iMike78/home-mini-DiP-v1/parts/MAX98357AETE_T.step

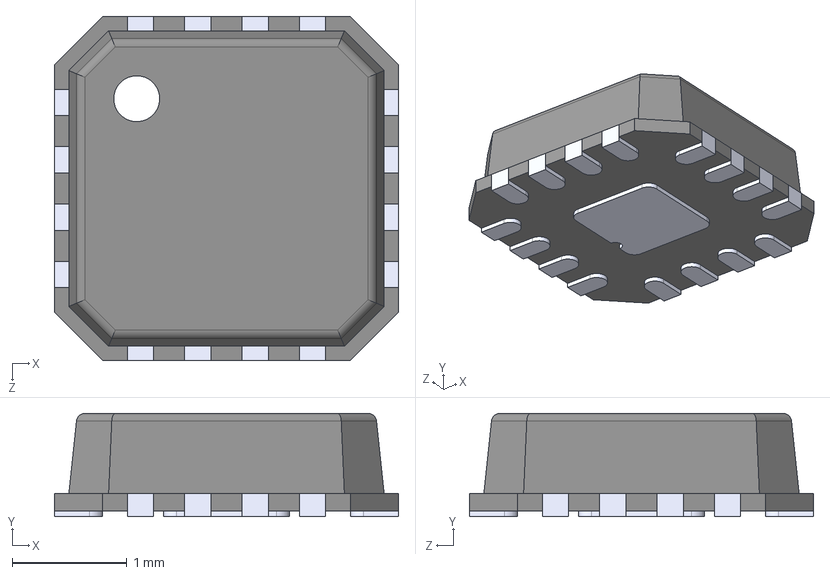
[picture p20: CAD file, 2025-12-22]
parts/MAX98357AETE_T.step
3.00 x 0.9 x 3.00 mm
