iMike78/home-mini-DiP-v1/parts/1775443-2.stp

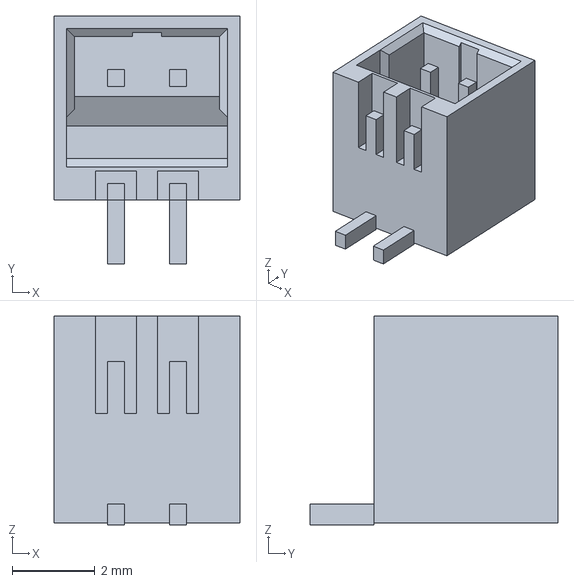
[picture p21: CAD file, 2025-12-22]
parts/1775443-2.stp
4.50 x 6.00 x 5.05 mm
