iMike78/home-mini-DiP-v1/audio.kicad_sch

## KiCad design audio.kicad_sch (2026-02-12)

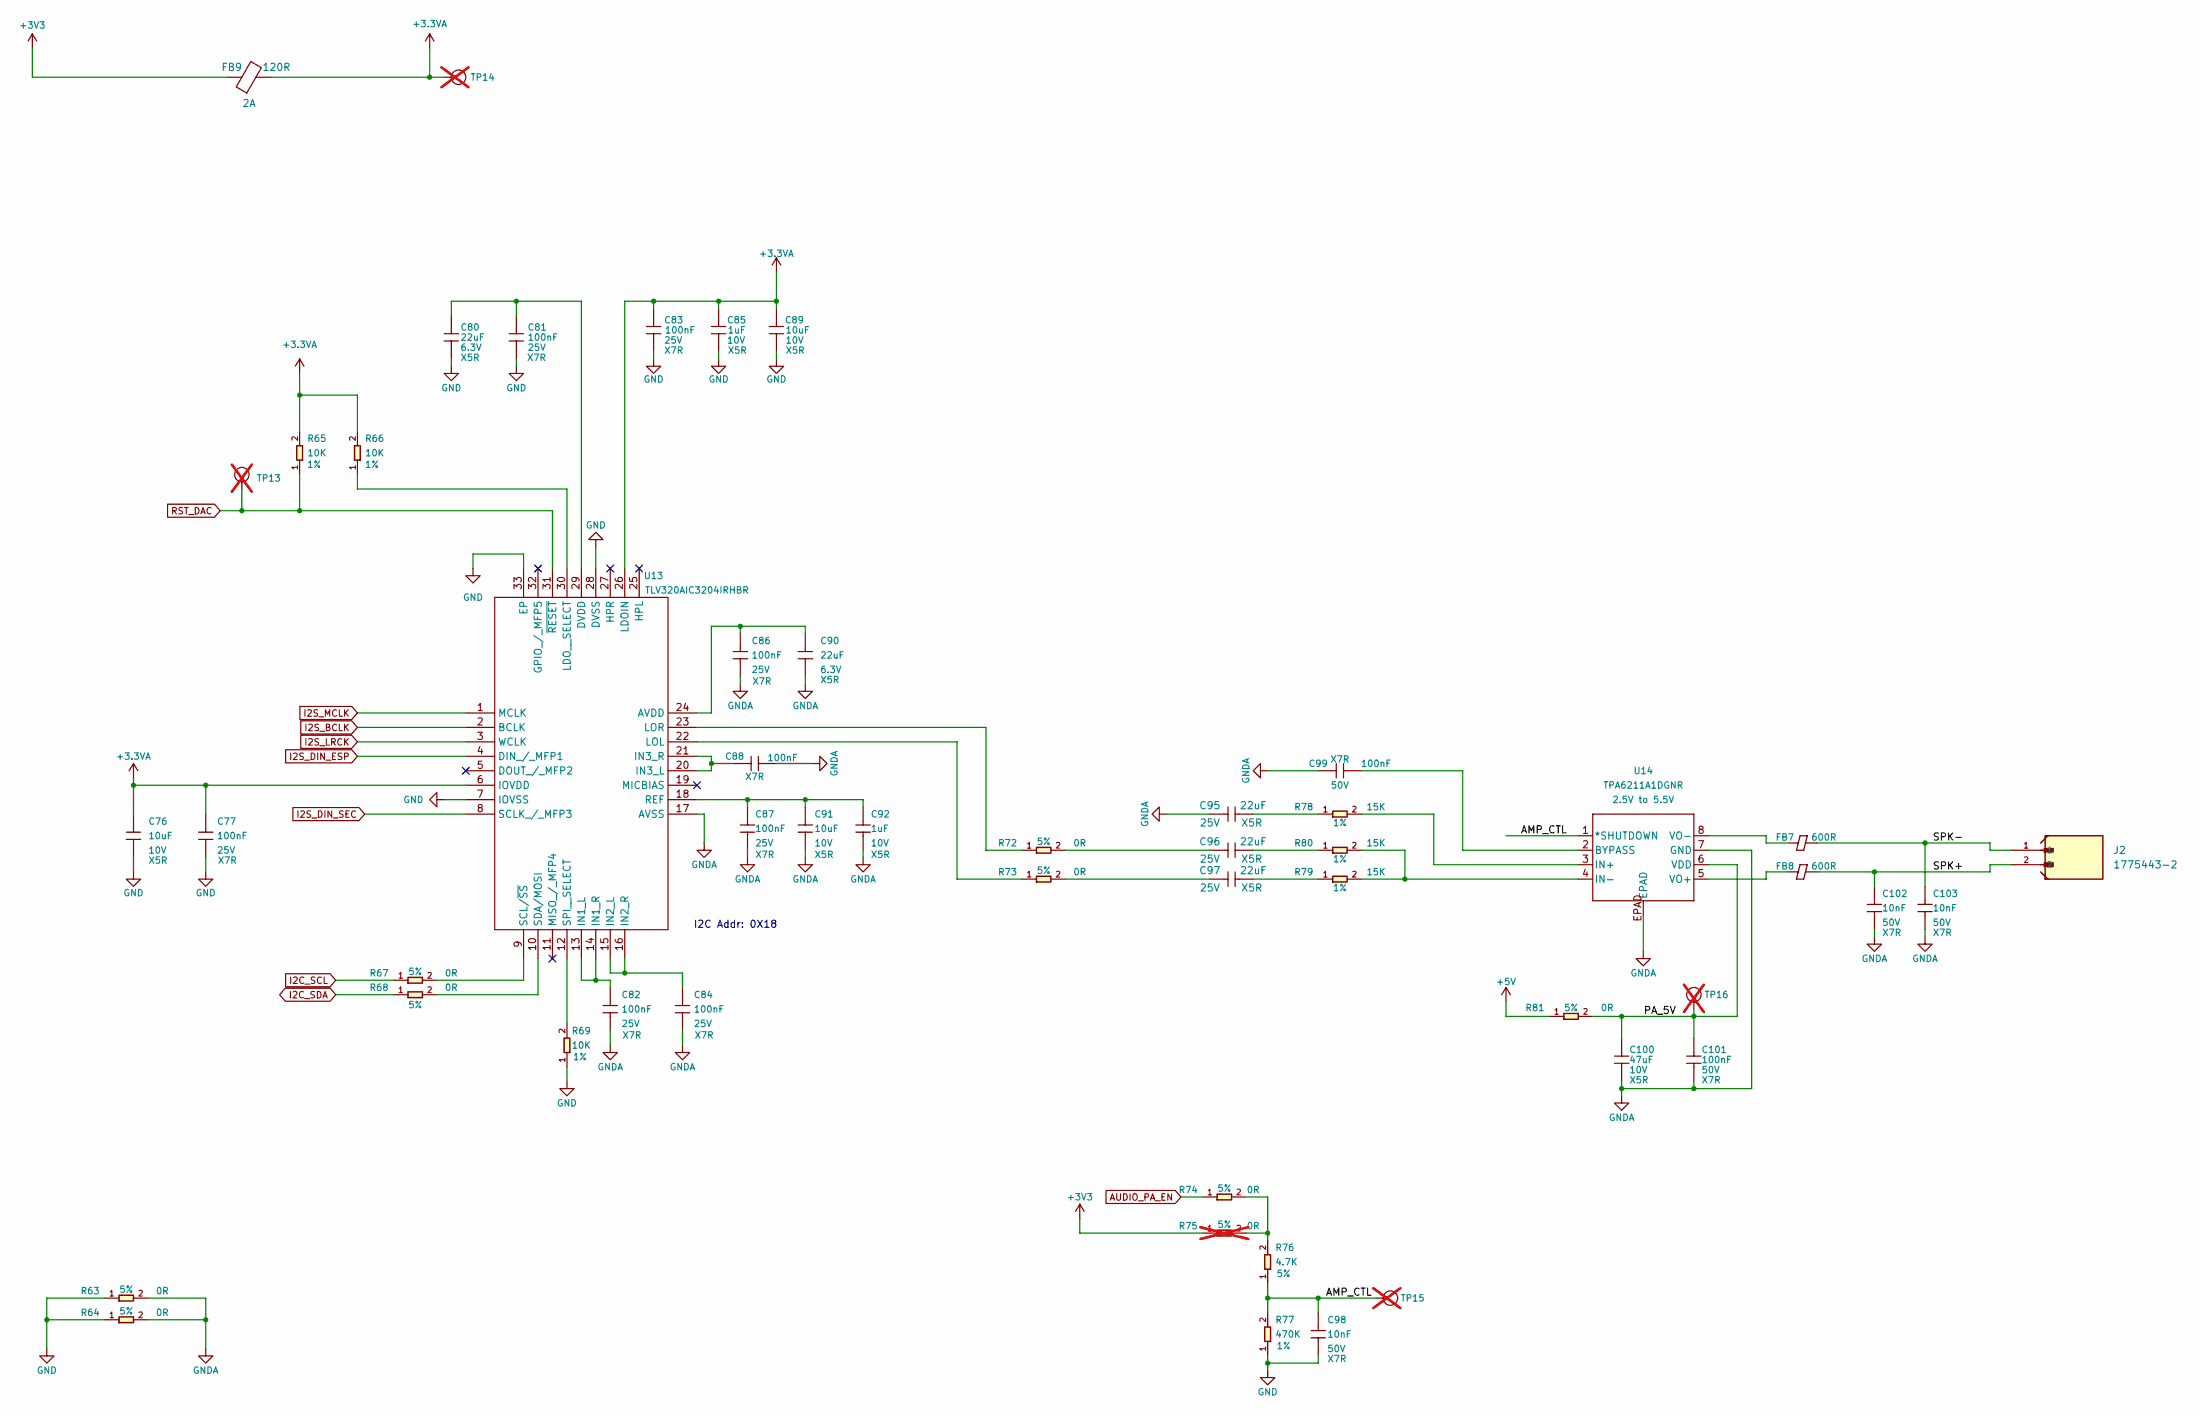
[picture p22: schematic audio.kicad_sch]

Parts:
C76, C89, C91: 10uF; C_0603_1608Metric; Voltage Rating 10V; Voltage 10V; MPN CL10A106KP8NNNC; LCSC Part # C19702
C77, C81, C82, C83, C84, C86, C87, C88: 100nF; C_0402_1005Metric; Voltage Rating 25V; Voltage 16V; MPN CL05B104KO5NNNC; LCSC Part # C1525
C80, C90: 22uF; C_0603_1608Metric; Voltage Rating 6.3V; Voltage 6.3V; MPN CL10A226MQ8NRNC; LCSC Part # C59461
C85, C92: 1uF; C_0402_1005Metric; Voltage Rating 10V; MPN CL05A105KA5NQNC; LCSC Part # C52923
C95, C96, C97: 22uF; C_0805_2012Metric; Voltage Rating 25V; Voltage 25V; MPN CL21A226MAQNNNE; LCSC Part # C45783
C98, C102, C103: 10nF; C_0402_1005Metric; Voltage Rating 50V; Voltage 50V; MPN CL05B103KB5NNNC; LCSC Part # C15195
C99, C101: 100nF; C_0603_1608Metric; Voltage Rating 50V; Voltage 50V; MPN CC0603KRX7R9BB104; LCSC Part # C14663
C100: 47uF; C_1206_3216Metric; Voltage Rating 10V; Voltage 10V; MPN CL31A476MPHNNNE; LCSC Part # C96123
FB7, FB8: 600R; BLM18PG121SN1D; Rating 500mA; MPN BLM18KG601SN1D; LCSC Part # C85833
FB9: 120R; BLM18PG121SN1D; Part number BLM18PG121SN1D; LCSC Part # C14709
J2: 1775443-2; PARTREV B5; LCSC Part # C5162845
R63, R64, R67, R68, R72, R73, R74: 0R; R_0402_1005Metric; Tolerance 5%; MPN 0402WGF0000TCE; LCSC Part # C17168
R65, R66, R69: 10K; R_0402_1005Metric; Tolerance 1%; MPN 0402WGF1002TCE; LCSC Part # C25744
R75: 0R; R_0402_1005Metric; Tolerance 5%; MPN RC0402JR-070RL; not fitted
R76: 4.7K; R_0402_1005Metric; Tolerance 5%; MPN 0402WGF4701TCE; LCSC Part # C25900
R77: 470K; R_0402_1005Metric; Tolerance 1%; Manufacturer Part 0402WGF4703TCE; LCSC Part # C25790
R78, R79, R80: 15K; R_0603_1608Metric; Tolerance 1%; Manufacturer Part 0603WAF1502T5E; LCSC Part # C22809
R81: 0R; R_0603_1608Metric; Tolerance 5%; Manufacturer Part 0603WAF0000T5E; LCSC Part # C21189
TP13, TP15: TEST-POINT; TestPoint_Pad_D1.0mm; not fitted
TP14, TP16: Test Point; TestPoint_Pad_D1.0mm; Part Type Test Point; not fitted
U13: TLV320AIC3204IRHBR; MPN TLV320AIC3204IRHBR; Mouser Part Number 595-V320AIC3204IRHBR
U14: TPA6211A1DGNR; Rating 2.5V to 5.5V; MPN TPA6211A1DGNR; LCSC Part # C7718

Connections:
+3.3VA: C76.1, C77.1, C83.1, C85.1, C89.1, FB9.2, R65.2, R66.2, TP14.1, U13.6 (IOVDD), U13.26 (LDOIN)
+3V3: FB9.1, R75.1
+5V: R81.1
AMP_CTL: C98.1, R76.1, R77.2, TP15.1, U14.1 (*SHUTDOWN)
AUDIO_PA_EN: R74.1
GND: C76.2, C77.2, C80.2, C81.2, C83.2, C85.2, C89.2, C98.2, R63.1, R64.1, R69.1, R77.1, U13.7 (IOVSS), U13.28 (DVSS), U13.33 (EP)
GNDA: C82.2, C84.2, C86.2, C87.2, C88.2, C90.2, C91.2, C92.2, C95.1, C99.1, C100.2, C101.2, C102.2, C103.2, R63.2, R64.2, U13.17 (AVSS), U14.7 (GND), U14.EPAD
I2C_SCL: R67.1
I2C_SDA: R68.1
I2S_BCLK: U13.2 (BCLK)
I2S_DIN_ESP: U13.4 (DIN_/_MFP1)
I2S_DIN_SEC: U13.8 (SCLK_/_MFP3)
I2S_LRCK: U13.3 (WCLK)
I2S_MCLK: U13.1 (MCLK)
unnamed: C80.1, C81.1, U13.29 (DVDD)
unnamed: C82.1, U13.13 (IN1_L), U13.14 (IN1_R)
unnamed: C84.1, U13.15 (IN2_L), U13.16 (IN2_R)
unnamed: C86.1, C90.1, U13.24 (AVDD)
unnamed: C87.1, C91.1, C92.1, U13.18 (REF)
unnamed: C88.1, U13.20 (IN3_L), U13.21 (IN3_R)
unnamed: C95.2, R78.1
unnamed: C96.1, R72.2
unnamed: C96.2, R80.1
unnamed: C97.1, R73.2
unnamed: C97.2, R79.1
unnamed: C99.2, U14.2 (BYPASS)
unnamed: FB7.1, U14.8 (VO-)
unnamed: FB8.1, U14.5 (VO+)
unnamed: R66.1, U13.30 (LDO__SELECT)
unnamed: R67.2, U13.9 (SCL/~SS)
unnamed: R68.2, U13.10 (SDA/MOSI)
unnamed: R69.2, U13.12 (SPI__SELECT)
unnamed: R72.1, U13.23 (LOR)
unnamed: R73.1, U13.22 (LOL)
unnamed: R74.2, R75.2, R76.2
unnamed: R78.2, U14.3 (IN+)
unnamed: R79.2, R80.2, U14.4 (IN-)
PA_5V: C100.1, C101.1, R81.2, TP16.1, U14.6 (VDD)
RST_DAC: R65.1, TP13.1, U13.31 (~RESET)
SPK+: C102.1, FB8.2, J2.2
SPK-: C103.1, FB7.2, J2.1

Notes on the sheet:
I2C Addr: 0X18
