iMike78/home-mini-DiP-v1/esp32.kicad_sch

## KiCad design esp32.kicad_sch (2026-02-12)

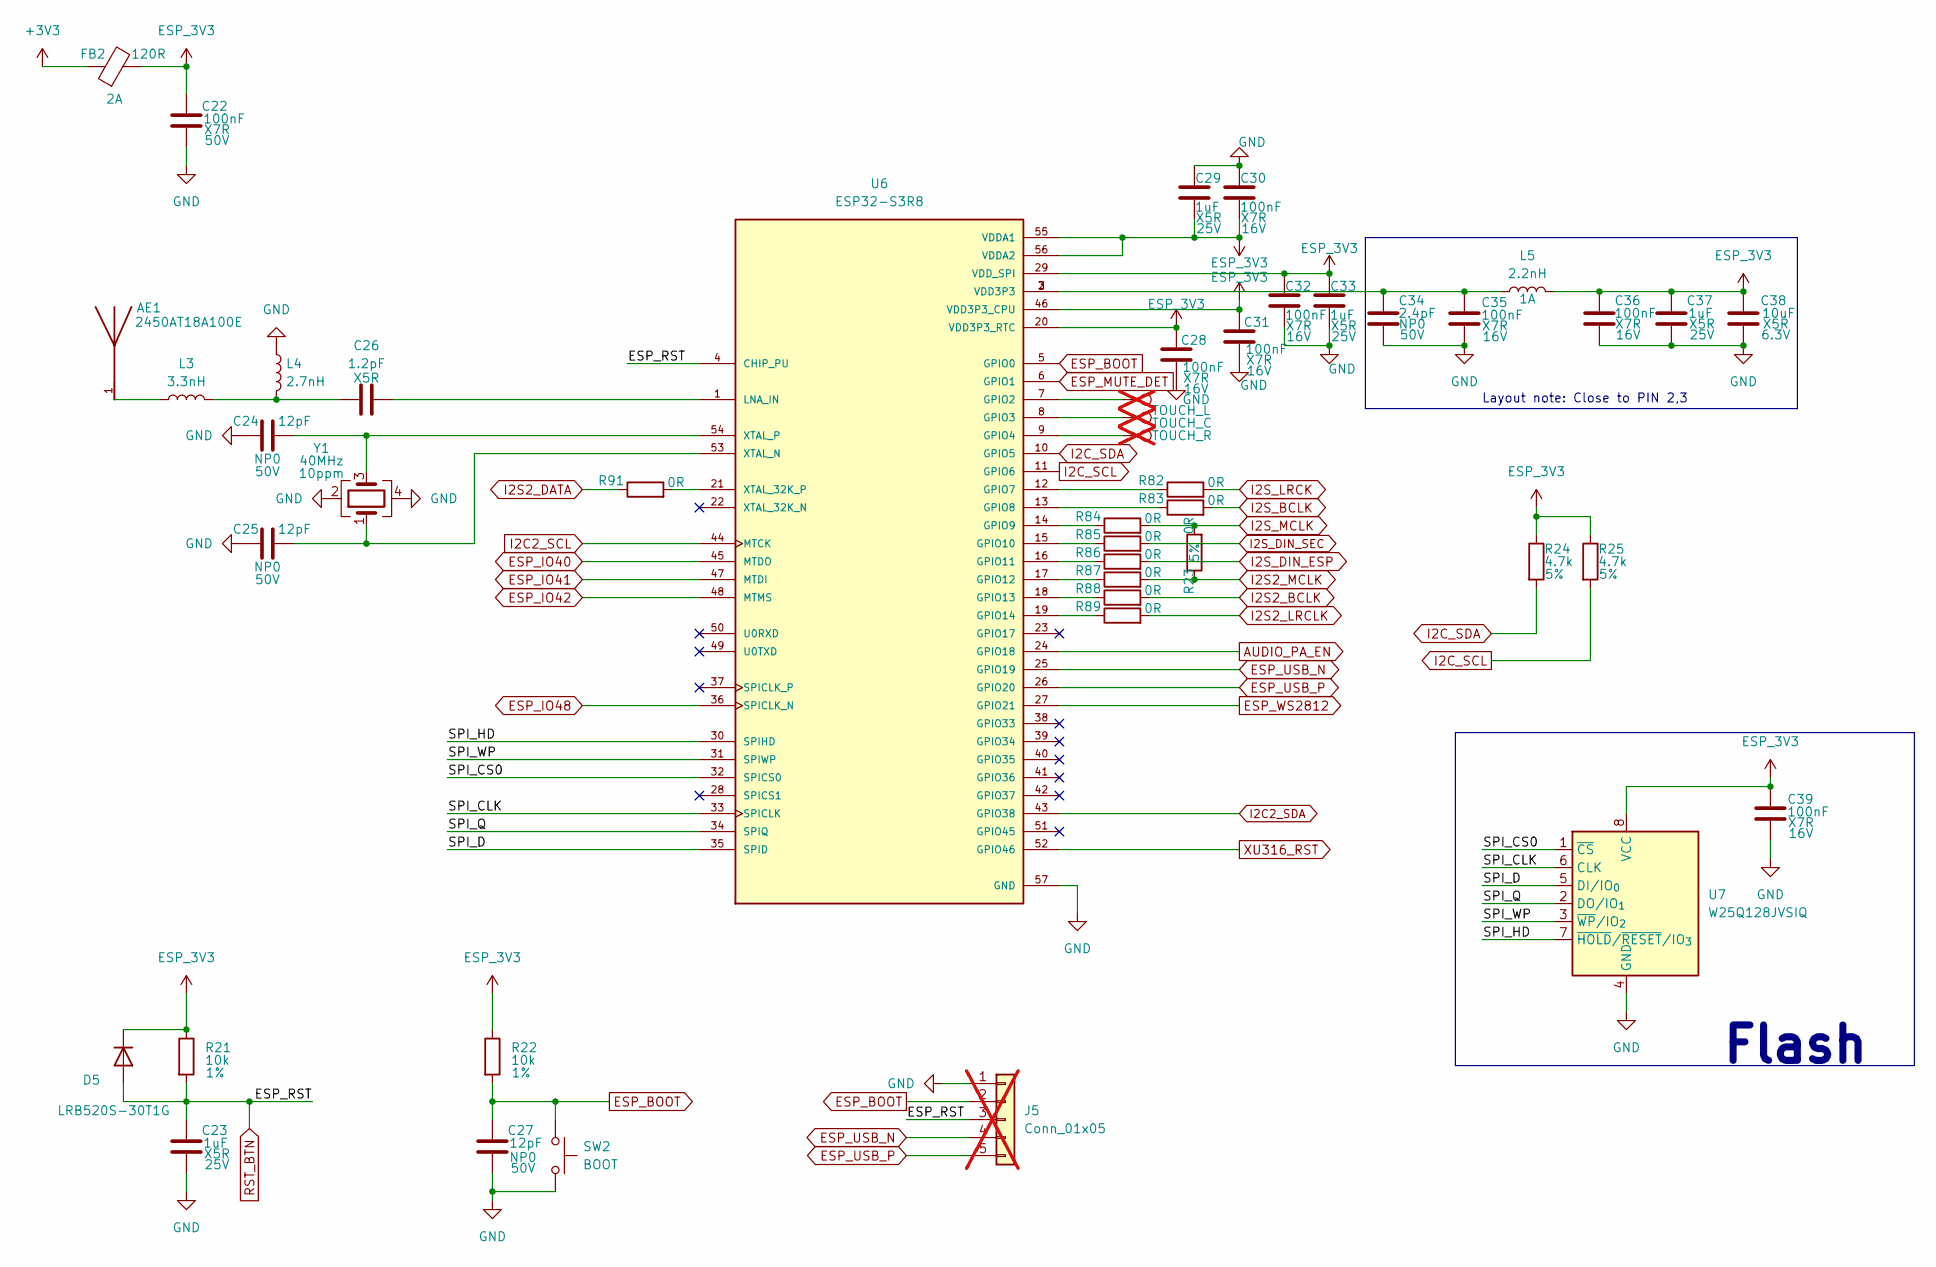
[picture p23: schematic esp32.kicad_sch]

Parts:
AE1: 2450AT18A100E; Johanson_2450AT18x100; PARTREV 1.3; LCSC Part # C89334
C22: 100nF; C_0603_1608Metric; Voltage 50V; Manufacturer Part CC0603KRX7R9BB104; LCSC Part # C14663
C23, C29, C33, C37: 1uF; C_0402_1005Metric; Voltage 25V; Manufacturer Part CL05A105KA5NQNC; LCSC Part # C52923
C24, C25, C27: 12pF; C_0402_1005Metric; Voltage 50V; Manufacturer Part 0402CG120J500NT; LCSC Part # C1547
C26: 1.2pF; C_0402_1005Metric; Voltage 10V; Manufacturer Part CC0402BRNPO9BN1R2; LCSC Part # C327292
C28, C30, C31, C32, C35, C36, C39: 100nF; C_0402_1005Metric; Voltage 16V; Manufacturer Part CL05B104KO5NNNC; LCSC Part # C1525
C34: 2.4pF; C_0402_1005Metric; Voltage 50V; Manufacturer Part 0402CG2R4C500NT; LCSC Part # C48346
C38: 10uF; C_0402_1005Metric; Voltage 6.3V; Manufacturer Part CL05A106MQ5NUNC; LCSC Part # C15525
D5: LRB520S-30T1G; D_SOD-523; Manufacturer Part LRB520S-30T1G; LCSC Part # C83680
FB2: 120R; BLM18PG121SN1D; Part number BLM18PG121SN1D; LCSC Part # C14709
J5: Conn_01x05; PinHeader_1x05_P2.54mm_Vertical; not fitted
L3: 3.3nH; L_0402_1005Metric; Manufacturer Part SDCL1005C3N3STDF; LCSC Part # C16526
L4: 2.7nH; L_0402_1005Metric; Manufacturer Part MHQ1005P2N7BT000; LCSC Part # C434826
L5: 2.2nH; L_0402_1005Metric; Manufacturer Part LQG15HS2N2B02D; LCSC Part # C162540
R21, R22: 10k; R_0402_1005Metric; Tolerance 1%; Manufacturer Part 0402WGF1002TCE; LCSC Part # C25744
R23, R82, R83, R84, R85, R86, R87, R88, R89, R91: 0R; R_0402_1005Metric; Tolerance 5%; Manufacturer Part 0402WGF0000TCE; LCSC Part # C17168
R24, R25: 4.7k; R_0402_1005Metric; Tolerance 5%; Manufacturer Part 0402WGF4701TCE; LCSC Part # C25900
SW2: BOOT; SW-SMD_4P-L4.2-W3.2-P2.15-LS4.5; Manufacturer Part PTS810SJS250SMTRLFS; LCSC Part # C221897
TP6: TOUCH_L; TestPoint_Pad_2.5x2.5mm; not fitted
TP7: TOUCH_C; TestPoint_Pad_2.5x2.5mm; not fitted
TP8: TOUCH_R; TestPoint_Pad_2.5x2.5mm; not fitted
U6: ESP32-S3R8; QFN40P700X700X90-57N; Manufacturer Part ESP32-S3R8; LCSC Part # C2913194
U7: W25Q128JVSIQ; SOIC-8_5.3x5.3mm_P1.27mm; Manufacturer Part W25Q128JVSIQ; LCSC Part # C97521
Y1: 40MHz; Crystal_SMD_2016-4Pin_2.0x1.6mm; Tolerance 10ppm; Manufacturer Part TAXM40M4ZCBCDT2T; LCSC Part # C424431

Connections:
+3V3: FB2.1
AUDIO_PA_EN: U6.24 (GPIO18)
ESP_3V3: C22.1, C28.1, C29.2, C30.2, C31.1, C32.1, C33.1, C36.1, C37.1, C38.1, C39.1, D5.1 (K), FB2.2, L5.2, R21.1, R22.1, R24.1, R25.1, U6.20 (VDD3P3_RTC), U6.29 (VDD_SPI), U6.46 (VDD3P3_CPU), U6.55 (VDDA1), U6.56 (VDDA2), U7.8 (VCC)
ESP_BOOT: C27.1, J5.2, R22.2, SW2.1, U6.5 (GPIO0)
ESP_IO40: U6.45 (MTDO)
ESP_IO41: U6.47 (MTDI)
ESP_IO42: U6.48 (MTMS)
ESP_IO48: U6.36 (SPICLK_N)
ESP_MUTE_DET: U6.6 (GPIO1)
ESP_USB_N: J5.4, U6.25 (GPIO19)
ESP_USB_P: J5.5, U6.26 (GPIO20)
ESP_WS2812: U6.27 (GPIO21)
GND: C22.2, C23.2, C24.1, C25.1, C27.2, C28.2, C29.1, C30.1, C31.2, C32.2, C33.2, C34.2, C35.2, C36.2, C37.2, C38.2, C39.2, J5.1, L4.1, SW2.2, U6.57 (GND), U7.4 (GND), Y1.2, Y1.4
I2C2_SCL: U6.44 (MTCK)
I2C2_SDA: U6.43 (GPIO38)
I2C_SCL: R25.2, U6.11 (GPIO6)
I2C_SDA: R24.2, U6.10 (GPIO5)
I2S2_BCLK: R88.2
I2S2_DATA: R91.1
I2S2_LRCLK: R89.2
I2S2_MCLK: R23.1, R87.2
I2S_BCLK: R83.2
I2S_DIN_ESP: R86.2
I2S_DIN_SEC: R85.2
I2S_LRCK: R82.2
I2S_MCLK: R23.2, R84.2
unnamed: AE1.1, L3.1
unnamed: C24.2, U6.54 (XTAL_P), Y1.3
unnamed: C25.2, U6.53 (XTAL_N), Y1.1
unnamed: C26.1, L3.2, L4.2
unnamed: C26.2, U6.1 (LNA_IN)
unnamed: C34.1, C35.1, L5.1, U6.2 (VDD3P3), U6.3 (VDD3P3)
unnamed: R82.1, U6.12 (GPIO7)
unnamed: R83.1, U6.13 (GPIO8)
unnamed: R84.1, U6.14 (GPIO9)
unnamed: R85.1, U6.15 (GPIO10)
unnamed: R86.1, U6.16 (GPIO11)
unnamed: R87.1, U6.17 (GPIO12)
unnamed: R88.1, U6.18 (GPIO13)
unnamed: R89.1, U6.19 (GPIO14)
unnamed: R91.2, U6.21 (XTAL_32K_P)
unnamed: TP6.1, U6.7 (GPIO2)
unnamed: TP7.1, U6.8 (GPIO3)
unnamed: TP8.1, U6.9 (GPIO4)
RST_BTN: C23.1, D5.2 (A), J5.3, R21.2, U6.4 (CHIP_PU)
SPI_CLK: U6.33 (SPICLK), U7.6 (CLK)
SPI_CS0: U6.32 (SPICS0), U7.1 (~CS)
SPI_D: U6.35 (SPID), U7.5 (DI/IO_{0})
SPI_HD: U6.30 (SPIHD), U7.7 (~HOLD/~RESET/IO_{3})
SPI_Q: U6.34 (SPIQ), U7.2 (DO/IO_{1})
SPI_WP: U6.31 (SPIWP), U7.3 (~WP/IO_{2})
XU316_RST: U6.52 (GPIO46)

Notes on the sheet:
Flash
Layout note: Close to PIN 2,3
