iMike78/home-mini-DiP-v1/leds.kicad_sch

## KiCad design leds.kicad_sch (2026-01-06)

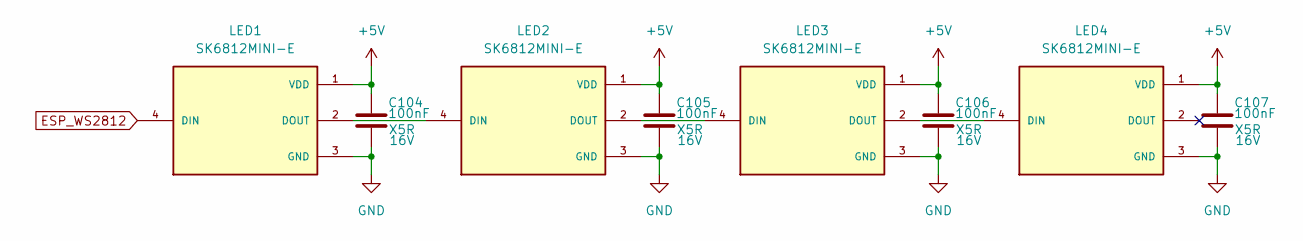
[picture p24: schematic leds.kicad_sch]

Parts:
C104, C105, C106, C107: 100nF; C_0402_1005Metric; Voltage 16V; Manufacturer Part CL05B104KO5NNNC; LCSC Part # C1525
LED1, LED2, LED3, LED4: SK6812MINI-E; PARTREV 2; LCSC Part # C5149201

Connections:
+5V: C104.1, C105.1, C106.1, C107.1, LED1.1 (VDD), LED2.1 (VDD), LED3.1 (VDD), LED4.1 (VDD)
ESP_WS2812: LED1.4 (DIN)
GND: C104.2, C105.2, C106.2, C107.2, LED1.3 (GND), LED2.3 (GND), LED3.3 (GND), LED4.3 (GND)
unnamed: LED1.2 (DOUT), LED2.4 (DIN)
unnamed: LED2.2 (DOUT), LED3.4 (DIN)
unnamed: LED3.2 (DOUT), LED4.4 (DIN)
