iMike78/home-mini-DiP-v1/power_handling.kicad_sch

## KiCad design power_handling.kicad_sch (2026-02-12)

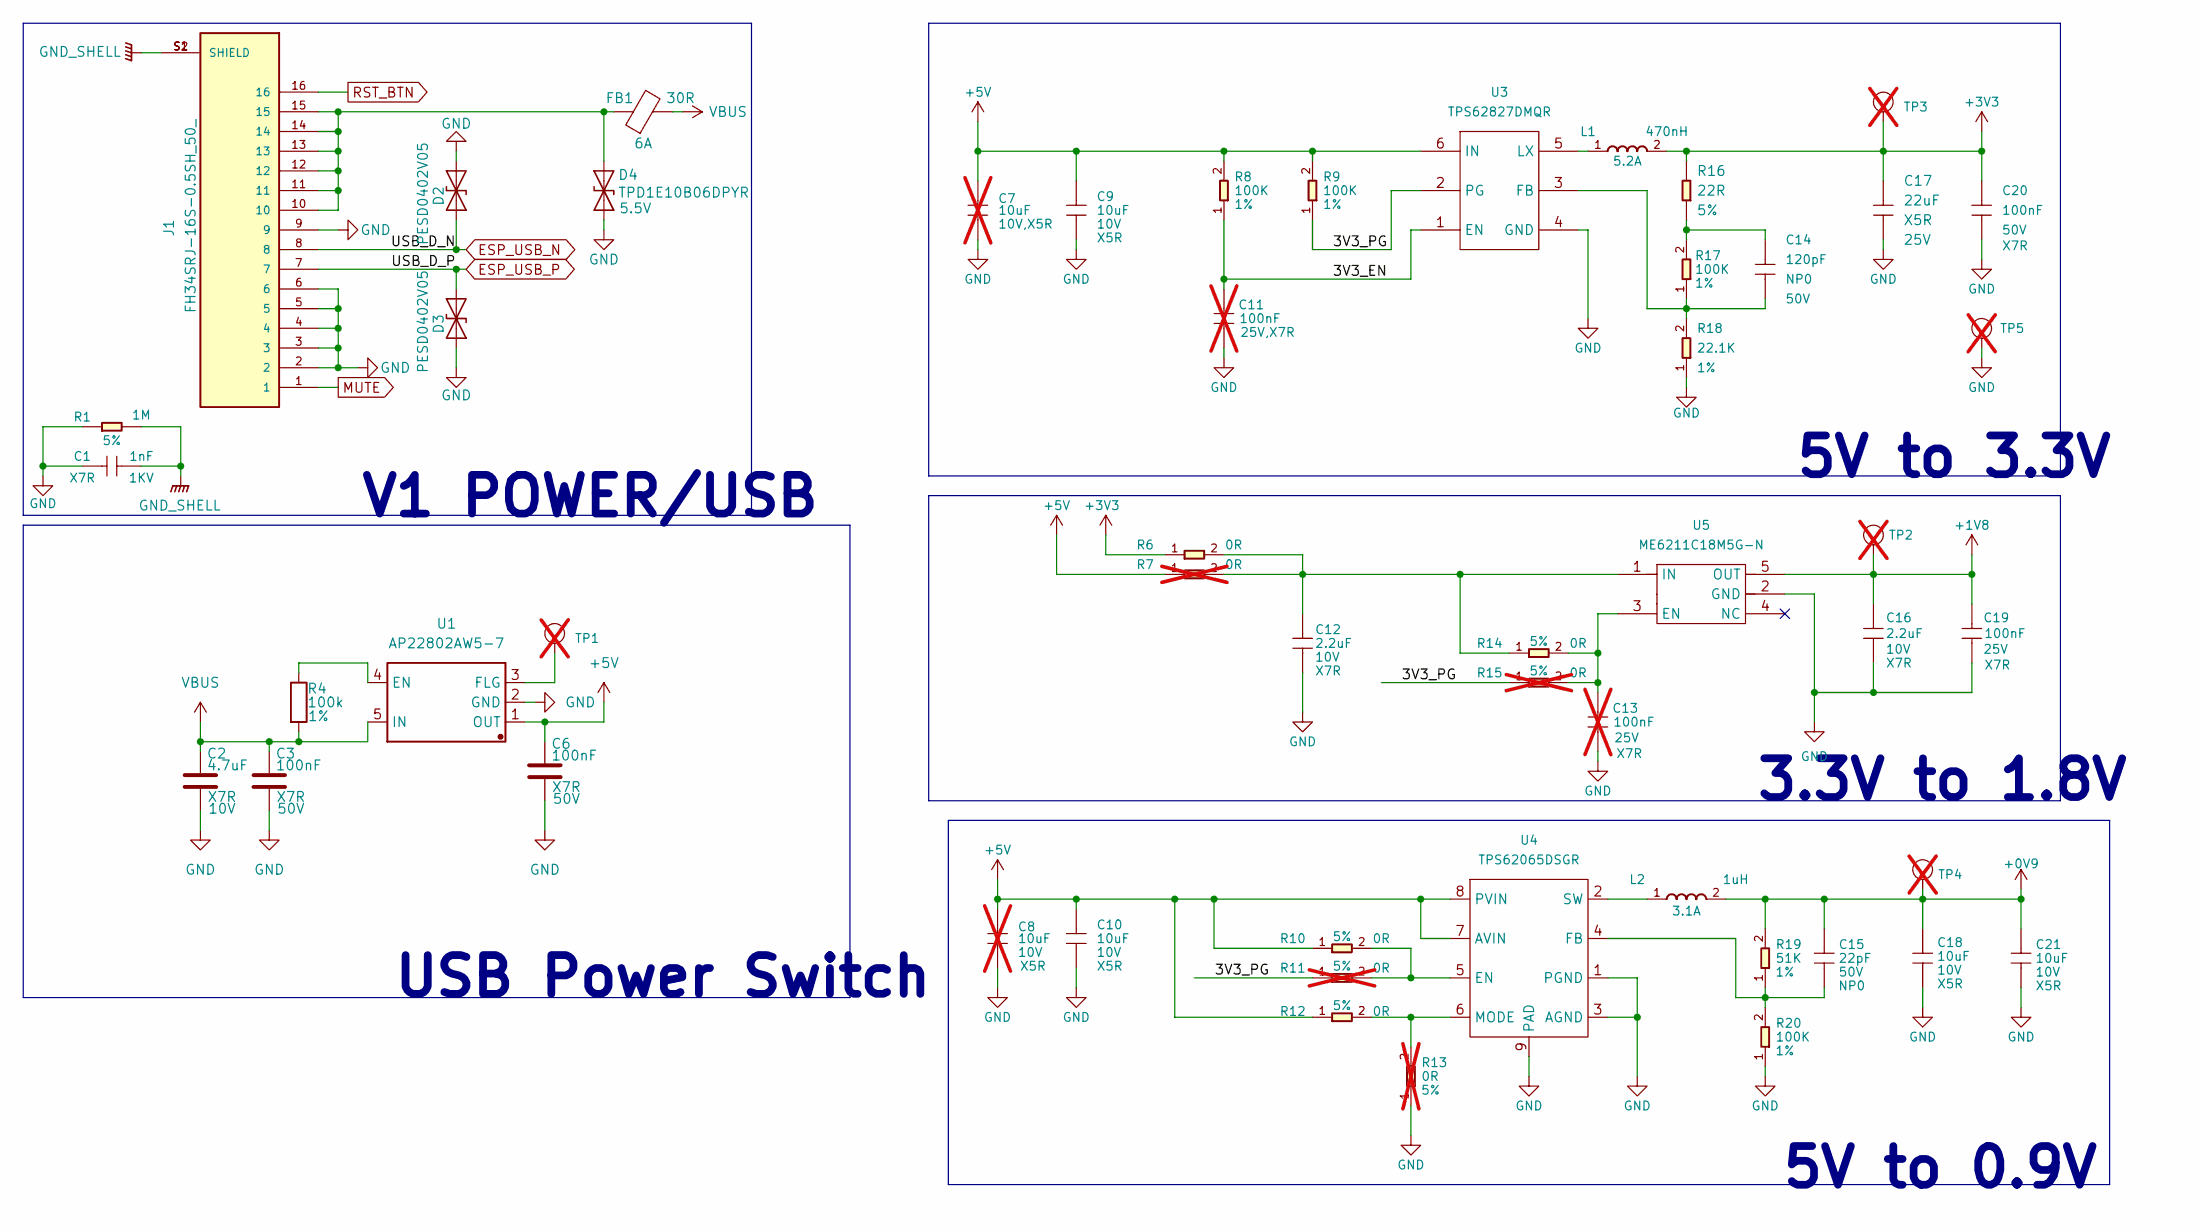
[picture p25: schematic power_handling.kicad_sch]

Parts:
C1: 1nF; C_1206_3216Metric; Voltage Rating 1KV; Voltage 2kV; MPN 1206B102K202NT; LCSC Part # C9196
C2: 4.7uF; C_0603_1608Metric; Voltage 10V; Manufacturer Part GRM188Z71A475KE15D; LCSC Part # C913474
C3, C6: 100nF; C_0603_1608Metric; Voltage 50V; Manufacturer Part CC0603KRX7R9BB104; LCSC Part # C14663
C7: 10uF; C_0603_1608Metric; Voltage Rating 10V,X5R; MPN CL10A106KP8NNNC; not fitted
C8: 10uF; C_0603_1608Metric; Voltage Rating 10V; MPN CL10A106KP8NNNC; not fitted
C9, C10, C18, C21: 10uF; C_0603_1608Metric; Voltage Rating 10V; Voltage 10V; MPN CL10A106KP8NNNC; LCSC Part # C19702
C11: 100nF; C_0402_1005Metric; Voltage Rating 25V,X7R; MPN CC0402KRX7R8BB104; not fitted
C12, C16: 2.2uF; C_0603_1608Metric; Voltage Rating 10V; Voltage 16V; MPN 0603B225K160NT; LCSC Part # C43922
C13: 100nF; C_0402_1005Metric; Voltage Rating 25V; MPN CC0402KRX7R8BB104; not fitted
C14: 120pF; C_0402_1005Metric; Voltage Rating 50V; Voltage 50V; MPN 0402CG121J500NT; LCSC Part # C40059
C15: 22pF; C_0402_1005Metric; Voltage Rating 50V; Voltage 50V; MPN 0402CG220J500NT; LCSC Part # C1555
C17: 22uF; C_0805_2012Metric; Voltage Rating 25V; Voltage 25V; MPN CL21A226MAQNNNE; LCSC Part # C45783
C19: 100nF; C_0402_1005Metric; Voltage Rating 25V; Voltage 16V; MPN CL05B104KO5NNNC; LCSC Part # C1525
C20: 100nF; C_0603_1608Metric; Voltage Rating 50V; Voltage 50V; MPN CC0603KRX7R9BB104; LCSC Part # C14663
D2, D3: PESD0402V05; D_0402_1005Metric; Manufacturer Part PESD0402V05; LCSC Part # C19626254
D4: TPD1E10B06DPYR; TPD1E05U06DPYR; Voltage 5.5V; Manufacturer Part TPD1E10B06DPYR; LCSC Part # C48260
FB1: 30R; BLM18PG300SN1D; Part number BLM18PG300SN1D; LCSC Part # C17305
J1: FH34SRJ-16S-0.5SH_50_; HRS_FH34SRJ-16S-0.5SH_50_; Manufacturer Part FH34SRJ-16S-0.5SH(50); LCSC Part # C324725
L1: 470nH; L0806; Rating 5.2A; MPN WPN201610MR47MT; LCSC Part # C97014
L2: 1uH; L_Murata_DFE201610P; Rating 3.1A; MPN WPN201610U1R0MTY01; LCSC Part # C395545
R1: 1M; R_0805_2012Metric; Power Rating 5%; MPN RC0805JR-071ML; LCSC Part # C107699
R4: 100k; R_0402_1005Metric; Tolerance 1%; Manufacturer Part 0402WGJ0104TCE; LCSC Part # C25530
R6, R10, R12, R14: 0R; R_0402_1005Metric; Tolerance 5%; MPN 0402WGF0000TCE; LCSC Part # C17168
R7, R11, R13, R15: 0R; R_0402_1005Metric; Tolerance 5%; MPN RC0402JR-070RL; not fitted
R8, R9, R17: 100K; R_0402_1005Metric; Power Rating 1%; MPN 0402WGJ0104TCE; LCSC Part # C25530
R16: 22R; R_0402_1005Metric; Power Rating 5%; MPN 0402WGF220JTCE; LCSC Part # C25092
R18: 22.1K; R_0402_1005Metric; Power Rating 1%; MPN 0402WGF2212TCE; LCSC Part # C43473
R19: 51K; R_0402_1005Metric; Tolerance 1%; MPN 0402WGF5102TCE; LCSC Part # C25794
R20: 100K; R_0402_1005Metric; Tolerance 1%; MPN 0402WGJ0104TCE; LCSC Part # C25530
TP1, TP2, TP3, TP4, TP5: TEST-POINT; TestPoint_Pad_D1.0mm; not fitted
U1: AP22802AW5-7; SOT-23-5; Manufacturer Part AP22802AW5-7; LCSC Part # C211404
U3: TPS62827DMQR; DFN6-0.5-1.5X1.5X0.65MM; MPN TPS62827DMQR; LCSC Part # C2071448
U4: TPS62065DSGR; MPN TPS62065DSGR; LCSC Part # C398352
U5: ME6211C18M5G-N; SOT-23-5; MPN ME6211C18M5G-N; LCSC Part # C236671

Connections:
3V3_EN: C11.1, R8.1, U3.1 (EN)
3V3_PG: R9.1, R11.1, R15.1, U3.2 (PG)
+0V9: C15.1, C18.1, C21.1, L2.2, R19.2, TP4.1
+1V8: C16.1, C19.1, TP2.1, U5.5 (OUT)
+3V3: C17.1, C20.1, L1.2, R6.1, R16.2, TP3.1
+5V: C6.1, C7.1, C8.1, C9.1, C10.1, R7.1, R8.2, R9.2, R10.1, R12.1, U1.1 (OUT), U3.6 (IN), U4.7 (AVIN), U4.8 (PVIN)
ESP_USB_N: D2.2 (A2), J1.8
ESP_USB_P: D3.1 (A1), J1.7
GND: C1.1, C2.2, C3.2, C6.2, C7.2, C8.2, C9.2, C10.2, C11.2, C12.2, C13.2, C16.2, C17.2, C18.2, C19.2, C20.2, C21.2, D2.1 (A1), D3.2 (A2), D4.1 (A1), J1.2, J1.3, J1.4, J1.5, J1.6, J1.9, R1.1, R13.1, R18.1, R20.1, TP5.1, U1.2 (GND), U3.4 (GND), U4.1 (PGND), U4.3 (AGND), U4.9 (PAD), U5.2 (GND)
GND_SHELL: C1.2, J1.S1 (SHIELD), J1.S2 (SHIELD), R1.2
MUTE: J1.1
unnamed: C12.1, R6.2, R7.2, R14.1, U5.1 (IN)
unnamed: C13.1, R14.2, R15.2, U5.3 (EN)
unnamed: C14.1, R16.1, R17.2
unnamed: C14.2, R17.1, R18.2, U3.3 (FB)
unnamed: C15.2, R19.1, R20.2, U4.4 (FB)
unnamed: D4.2 (A2), FB1.1, J1.10, J1.11, J1.12, J1.13, J1.14, J1.15
unnamed: L1.1, U3.5 (LX)
unnamed: L2.1, U4.2 (SW)
unnamed: R4.1, U1.4 (EN)
unnamed: R10.2, R11.2, U4.5 (EN)
unnamed: R12.2, R13.2, U4.6 (MODE)
unnamed: TP1.1, U1.3 (FLG)
RST_BTN: J1.16
VBUS: C2.1, C3.1, FB1.2, R4.2, U1.5 (IN)

Notes on the sheet:
V1 POWER/USB
USB Power Switch
3.3V to 1.8V
5V to 3.3V
5V to 0.9V
