iMike78/home-mini-DiP-v1/xmos.kicad_sch

## KiCad design xmos.kicad_sch (2026-02-12)

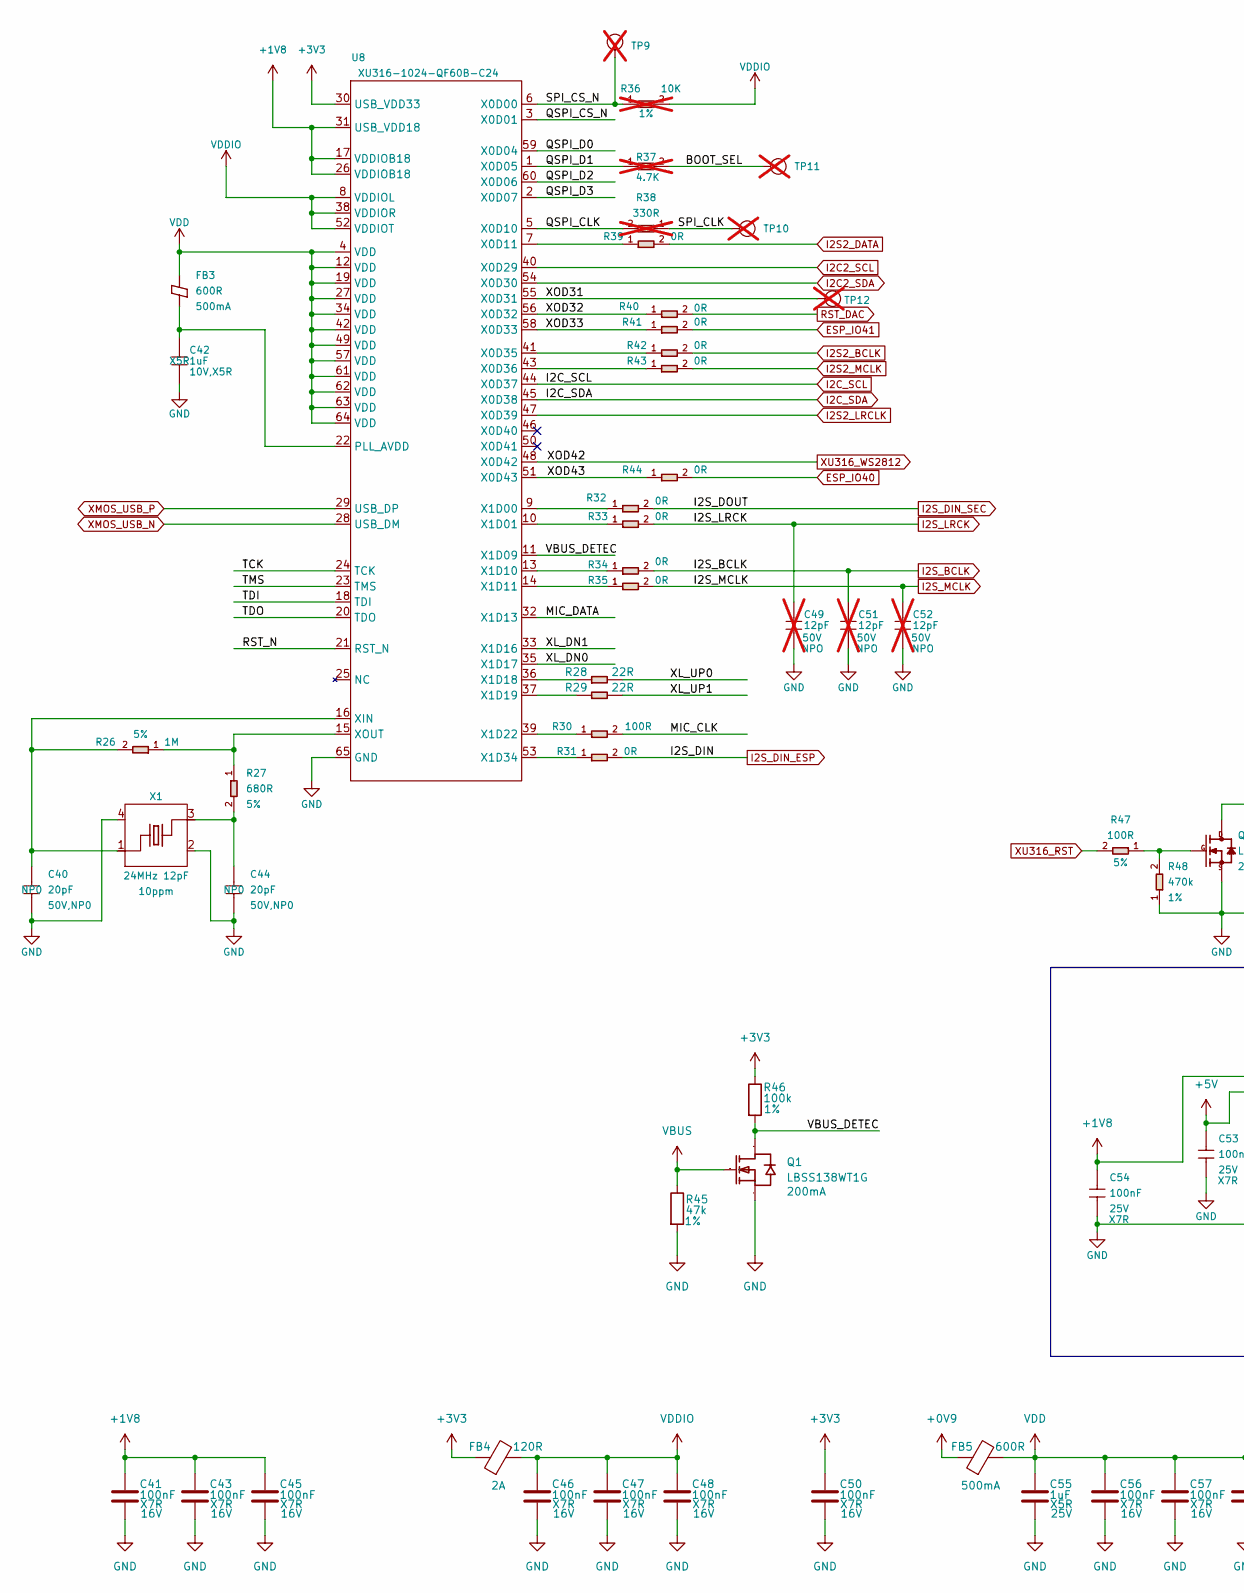
[picture p26: schematic xmos.kicad_sch, part in row 1, column 1]

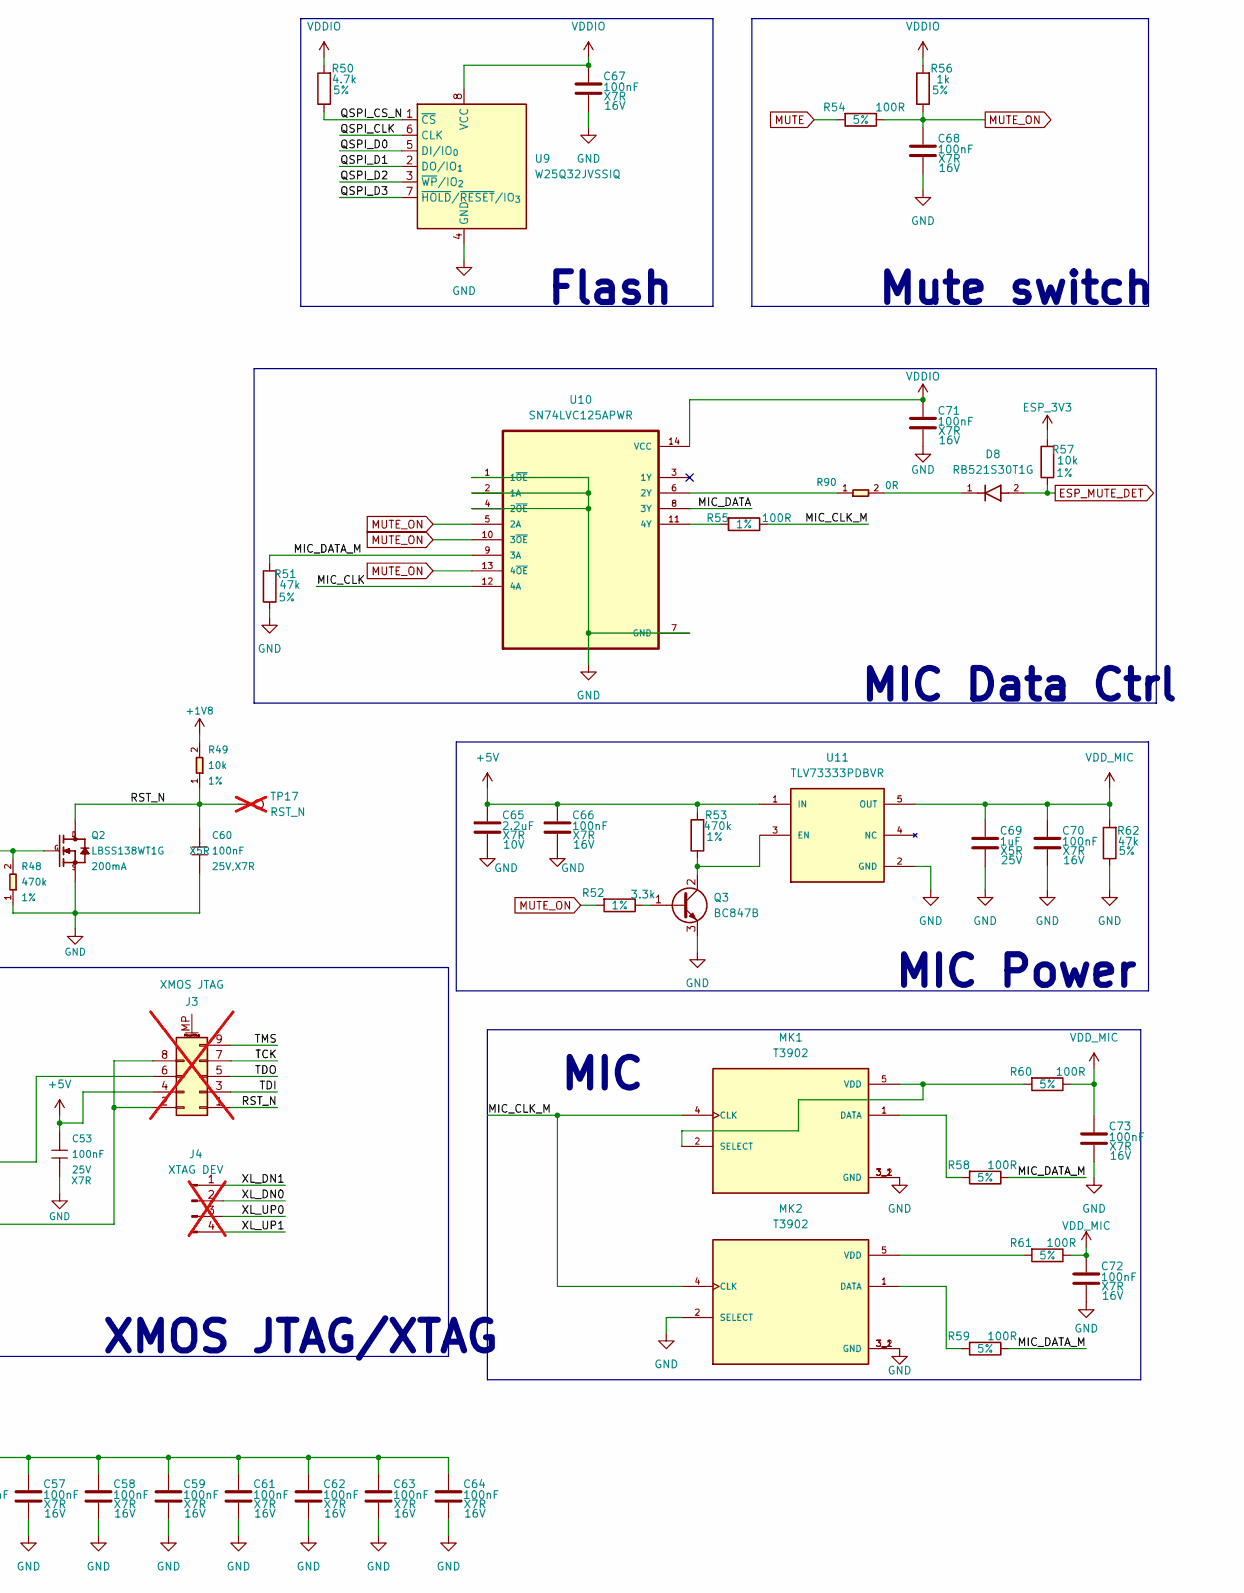
[picture p27: schematic xmos.kicad_sch, part in row 1, column 2]

Parts:
C40, C44: 20pF; C_0402_1005Metric; Voltage Rating 50V,NP0; Voltage 50V; MPN 0402CG200J500NT; LCSC Part # C1554
C41, C43, C45, C46, C47, C48, C50, C56, C57, C58, C59, C61, C62, C63, C64, C66, C67, C68, C70, C71, C72, C73: 100nF; C_0402_1005Metric; Voltage 16V; Manufacturer Part CL05B104KO5NNNC; LCSC Part # C1525
C42: 1uF; C_0402_1005Metric; Voltage Rating 10V,X5R; Voltage 25V; MPN CL05A105KA5NQNC; LCSC Part # C52923
C49, C51, C52: 12pF; C_0402_1005Metric; Voltage Rating 50V; MPN CC0402JRNPO9BN120; not fitted
C53, C54: 100nF; C_0402_1005Metric; Voltage Rating 25V; Voltage 16V; MPN CL05B104KO5NNNC; LCSC Part # C1525
C55, C69: 1uF; C_0402_1005Metric; Voltage 25V; Manufacturer Part CL05A105KA5NQNC; LCSC Part # C52923
C60: 100nF; C_0402_1005Metric; Voltage Rating 25V,X7R; MPN CL05B104KO5NNNC; LCSC Part # C1525
C65: 2.2uF; C_0603_1608Metric; Voltage 10V; Manufacturer Part GRM188R71A225KE15D; LCSC Part # C86018
D8: RB521S30T1G; DIOM168X70N; PARTREV 7/11/1905; LCSC Part # C27636108
FB3: 600R; BLM18PG121SN1D; Rating 500mA; MPN BLM18KG601SN1D; LCSC Part # C85833
FB4: 120R; BLM18PG121SN1D; Part number BLM18AG121SN1D; LCSC Part # C14709
FB5: 600R; BLM18PG121SN1D; Part number BLM18AG601SN1D; LCSC Part # C85833
J3: XMOS JTAG; PinHeader_2x05_P2.54mm_Vertical; not fitted
J4: XTAG DEV; PinHeader_1x04_P2.54mm_Vertical; not fitted
MK1, MK2: T3902; MIC_T3902; PARTREV 1.0; LCSC Part # C3171752
Q1: LBSS138WT1G; SOT-323_SC-70; Manufacturer Part LBSS138WT1G; LCSC Part # C383201
Q2: LBSS138WT1G; SOT-323_SC-70; Rating 200mA; MPN LBSS138WT1G; LCSC Part # C383201
Q3: BC847B; SOT-23; Manufacturer Part BC847B; LCSC Part # C20069135
R26: 1M; R_0402_1005Metric; Power Rating 5%; MPN 0402WGF1004TCE; LCSC Part # C26083
R27: 680R; R_0402_1005Metric; Power Rating 5%; MPN 0402WGF6800TCE; LCSC Part # C25130
R28, R29: 22R; R_0402_1005Metric; Power Rating 5%; MPN 0402WGF220JTCE; LCSC Part # C25092
R30, R47: 100R; R_0402_1005Metric; Power Rating 5%; MPN 0402WGF1000TCE; LCSC Part # C25076
R31, R32, R33, R34, R35, R41, R42, R43, R44: 0R; R_0402_1005Metric; Power Rating 5%; MPN 0402WGF0000TCE; LCSC Part # C17168
R36: 10K; R_0402_1005Metric; Power Rating 1%; MPN RC0402FR-0710KL; not fitted
R37: 4.7K; R_0402_1005Metric; Tolerance 5%; MPN RC0402JR-074K7L; not fitted
R38: 330R; R_0402_1005Metric; Tolerance 1%; MPN RC0402FR-07330RL; not fitted
R39, R40, R90: 0R; R_0402_1005Metric; Tolerance 5%; MPN 0402WGF0000TCE; LCSC Part # C17168
R45: 47k; R_0402_1005Metric; Tolerance 1%; Manufacturer Part 0402WGF4702TCE; LCSC Part # C25792
R46: 100k; R_0402_1005Metric; Tolerance 1%; Manufacturer Part 0402WGJ0104TCE; LCSC Part # C25530
R48: 470k; R_0402_1005Metric; Power Rating 1%; MPN 0402WGF4703TCE; LCSC Part # C25790
R49: 10k; R_0402_1005Metric; Power Rating 1%; MPN 0402WGF1002TCE; LCSC Part # C25744
R50: 4.7k; R_0402_1005Metric; Tolerance 5%; Manufacturer Part 0402WGF4701TCE; LCSC Part # C25900
R51, R62: 47k; R_0402_1005Metric; Tolerance 5%; Manufacturer Part 0402WGF4702TCE; LCSC Part # C25792
R52: 3.3k; R_0402_1005Metric; Tolerance 1%; Manufacturer Part 0402WGF3301TCE; LCSC Part # C25890
R53: 470k; R_0402_1005Metric; Tolerance 1%; Manufacturer Part 0402WGF4703TCE; LCSC Part # C25790
R54, R58, R59, R60, R61: 100R; R_0402_1005Metric; Tolerance 5%; Manufacturer Part 0402WGF1000TCE; LCSC Part # C25076
R55: 100R; R_0402_1005Metric; Tolerance 1%; Manufacturer Part 0402WGF1000TCE; LCSC Part # C25076
R56: 1k; R_0402_1005Metric; Tolerance 5%; Manufacturer Part 0402WGF1001TCE; LCSC Part # C11702
R57: 10k; R_0402_1005Metric; Tolerance 1%; Manufacturer Part 0402WGF1002TCE; LCSC Part # C25744
TP9, TP10, TP11: TEST-POINT; TestPoint_Pad_D1.0mm; not fitted
TP12: Test Point; TestPoint_Pad_D1.0mm; Part Type Test Point; not fitted
TP17: RST_N; TestPoint_Pad_D1.0mm; not fitted
U8: XU316-1024-QF60B-C24 ; XU316-1024-QF60B-C24; MPN XU316-1024-QF60B-C24; LCSC Part # C6617472
U9: W25Q32JVSSIQ; SOIC-8_5.3x5.3mm_P1.27mm; Manufacturer Part W25Q32JVSSIQ; LCSC Part # C179173
U10: SN74LVC125APWR; SOP65P640X120-14N; Manufacturer Part SN74LVC125APWR; LCSC Part # C7813
U11: TLV73333PDBVR; PARTREV C; LCSC Part # C134139
X1: 24MHz 12pF; X4-SMD-2.0X1.6MM; Rating 10ppm; MPN 7F24000E12UCG; LCSC Part # C252273

Connections:
+0V9: FB5.1
+1V8: C41.1, C43.1, C45.1, C54.1, J3.6, R49.2, U8.17 (VDDIOB18), U8.26 (VDDIOB18), U8.31 (USB_VDD18)
+3V3: C50.1, FB4.1, R46.1, U8.30 (USB_VDD33)
+5V: C53.1, C65.1, C66.1, J3.4, R53.2, U11.1 (IN)
BOOT_SEL: R37.2, TP11.1
ESP_3V3: R57.2
ESP_IO40: R44.2
ESP_IO41: R41.2
ESP_MUTE_DET: D8.2, R57.1
GND: C40.2, C41.2, C42.2, C43.2, C44.2, C45.2, C46.2, C47.2, C48.2, C49.2, C50.2, C51.2, C52.2, C53.2, C54.2, C55.2, C56.2, C57.2, C58.2, C59.2, C60.2, C61.2, C62.2, C63.2, C64.2, C65.2, C66.2, C67.2, C68.2, C69.2, C70.2, C71.2, C72.2, C73.2, J3.2, J3.8, MK1.3_1 (GND), MK1.3_2 (GND), MK2.2 (SELECT), MK2.3_1 (GND), MK2.3_2 (GND), Q1.2 (S), Q2.2 (S), Q3.3 (E), R45.2, R48.1, R51.1, R62.1, U8.65 (GND), U9.4 (GND), U10.1 (1~OE), U10.2 (1A), U10.4 (2~OE), U10.7 (GND), U11.2 (GND), X1.2, X1.4
I2C2_SCL: U8.40 (X0D29)
I2C2_SDA: U8.54 (X0D30)
I2C_SCL: U8.44 (X0D37)
I2C_SDA: U8.45 (X0D38)
I2S2_BCLK: R42.2
I2S2_DATA: R39.2
I2S2_LRCLK: U8.47 (X0D39)
I2S2_MCLK: R43.2
I2S_BCLK: C51.1, R34.2
I2S_DIN_ESP: R31.2
I2S_DIN_SEC: R32.2
I2S_LRCK: C49.1, R33.2
I2S_MCLK: C52.1, R35.2
MIC_CLK: R30.2, U10.12 (4A)
MIC_CLK_M: MK1.4 (CLK), MK2.4 (CLK), R55.1
MIC_DATA: U8.32 (X1D13), U10.8 (3Y)
MIC_DATA_M: R51.2, R58.1, R59.1, U10.9 (3A)
MUTE: R54.2
MUTE_ON: C68.1, R52.2, R54.1, R56.1, U10.5 (2A), U10.10 (3~OE), U10.13 (4~OE)
unnamed: C40.1, R26.2, U8.16 (XIN), X1.1
unnamed: C42.1, FB3.1, U8.22 (PLL_AVDD)
unnamed: C44.1, R27.2, X1.3
unnamed: D8.1, R90.2
unnamed: MK1.1 (DATA), R58.2
unnamed: MK1.2 (SELECT), MK1.5 (VDD), R60.2
unnamed: MK2.1 (DATA), R59.2
unnamed: MK2.5 (VDD), R61.2
unnamed: Q2.1 (G), R47.1, R48.2
unnamed: Q3.1 (B), R52.1
unnamed: Q3.2 (C), R53.1, U11.3 (EN)
unnamed: R26.1, R27.1, U8.15 (XOUT)
unnamed: R28.1, U8.36 (X1D18)
unnamed: R29.1, U8.37 (X1D19)
unnamed: R30.1, U8.39 (X1D22)
unnamed: R31.1, U8.53 (X1D34)
unnamed: R32.1, U8.9 (X1D00)
unnamed: R33.1, U8.10 (X1D01)
unnamed: R34.1, U8.13 (X1D10)
unnamed: R35.1, U8.14 (X1D11)
unnamed: R39.1, U8.7 (X0D11)
unnamed: R42.1, U8.41 (X0D35)
unnamed: R43.1, U8.43 (X0D36)
unnamed: R55.2, U10.11 (4Y)
unnamed: R90.1, U10.6 (2Y)
QSPI_CLK: R38.2, U8.5 (X0D10), U9.6 (CLK)
QSPI_CS_N: R50.1, U8.3 (X0D01), U9.1 (~CS)
QSPI_D0: U8.59 (X0D04), U9.5 (DI/IO_{0})
QSPI_D1: R37.1, U8.1 (X0D05), U9.2 (DO/IO_{1})
QSPI_D2: U8.60 (X0D06), U9.3 (~WP/IO_{2})
QSPI_D3: U8.2 (X0D07), U9.7 (~HOLD/~RESET/IO_{3})
RST_DAC: R40.2
RST_N: C60.1, J3.1, Q2.3 (D), R49.1, TP17.1, U8.21 (RST_N)
SPI_CLK: R38.1, TP10.1
SPI_CS_N: R36.1, TP9.1, U8.6 (X0D00)
TCK: J3.7, U8.24 (TCK)
TDI: J3.3, U8.18 (TDI)
TDO: J3.5, U8.20 (TDO)
TMS: J3.9, U8.23 (TMS)
VBUS: Q1.1 (G), R45.1
VBUS_DETEC: Q1.3 (D), R46.2, U8.11 (X1D09)
VDD: C55.1, C56.1, C57.1, C58.1, C59.1, C61.1, C62.1, C63.1, C64.1, FB3.2, FB5.2, U8.4 (VDD), U8.12 (VDD), U8.19 (VDD), U8.27 (VDD), U8.34 (VDD), U8.42 (VDD), U8.49 (VDD), U8.57 (VDD), U8.61 (VDD), U8.62 (VDD), U8.63 (VDD), U8.64 (VDD)
VDDIO: C46.1, C47.1, C48.1, C67.1, C71.1, FB4.2, R36.2, R50.2, R56.2, U8.8 (VDDIOL), U8.38 (VDDIOR), U8.52 (VDDIOT), U9.8 (VCC), U10.14 (VCC)
VDD_MIC: C69.1, C70.1, C72.1, C73.1, R60.1, R61.1, R62.2, U11.5 (OUT)
XL_DN0: J4.2, U8.35 (X1D17)
XL_DN1: J4.1, U8.33 (X1D16)
XL_UP0: J4.3, R28.2
XL_UP1: J4.4, R29.2
XMOS_USB_N: U8.28 (USB_DM)
XMOS_USB_P: U8.29 (USB_DP)
XOD31: TP12.1, U8.55 (X0D31)
XOD32: R40.1, U8.56 (X0D32)
XOD33: R41.1, U8.58 (X0D33)
XOD43: R44.1, U8.51 (X0D43)
XU316_RST: R47.2
XU316_WS2812: U8.48 (X0D42)

Notes on the sheet:
Flash
MIC
Mute switch
MIC Power
MIC Data Ctrl
XMOS JTAG/XTAG
